3dprogramin/home-alarm/schematics/home-alarm/home-alarm.kicad_sch

## KiCad design schematics/home-alarm/home-alarm.kicad_sch (2024-11-03)

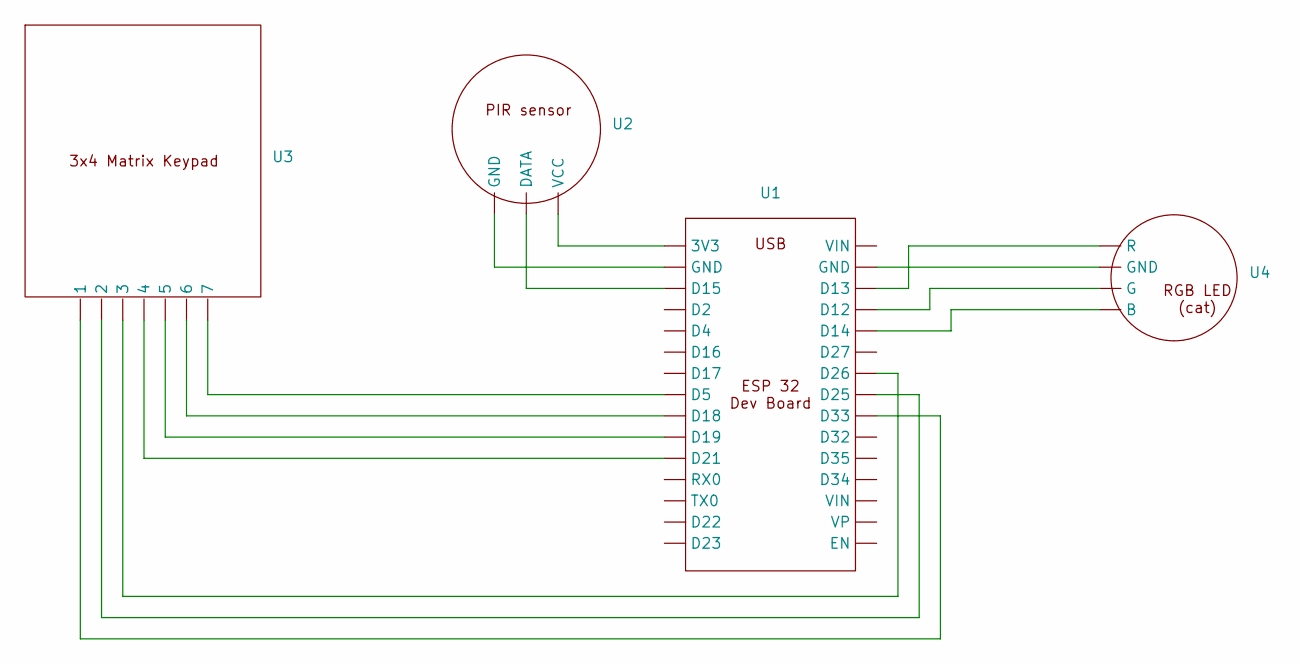
[picture p8: schematic home-alarm.kicad_sch]

Parts:
U1, U2, U3, U4: (no value)

Connections:
unnamed: U1., U2., U3., U4.
